Fourthlaw/holler/hardware/inwall/renders/render_carrier_back.png

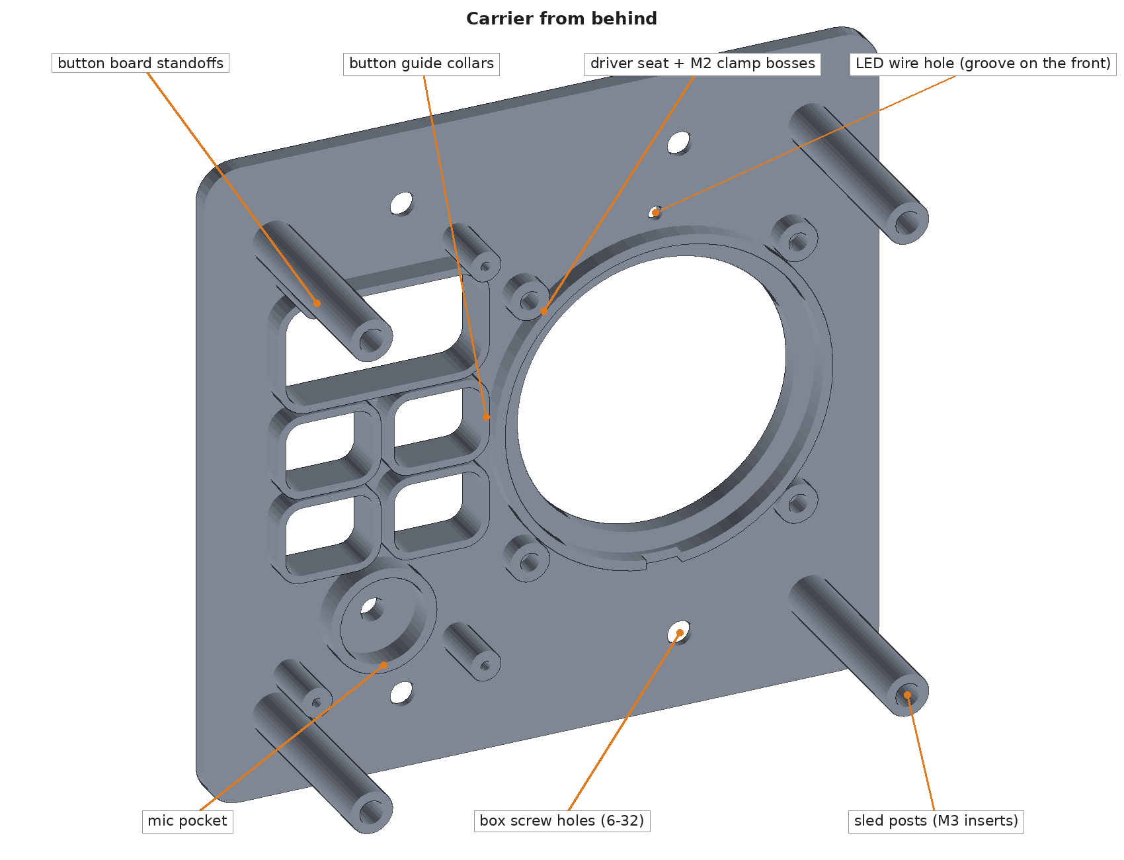
hardware/inwall/renders/render_carrier_back.png
