Fourthlaw/holler/hardware/tabletop/renders/render_base_iso.png

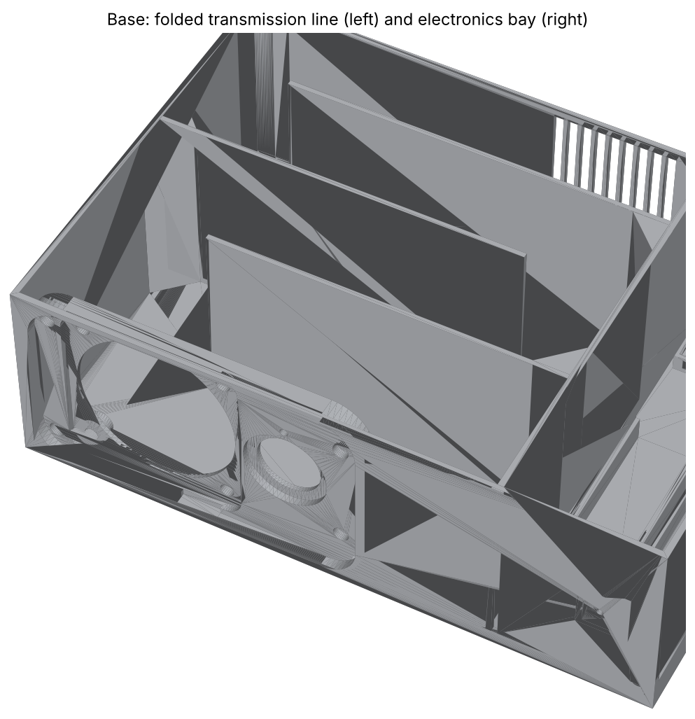
hardware/tabletop/renders/render_base_iso.png
